kallikak/Mentor/teensy/LFOShape.png

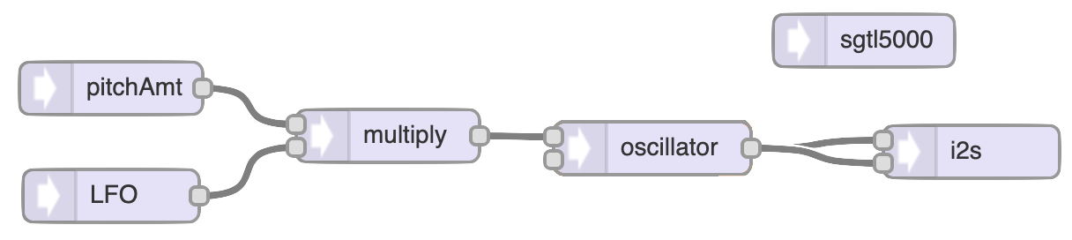
teensy/LFOShape.png
