kallikak/Mentor/teensy/WaveTypeMix.png

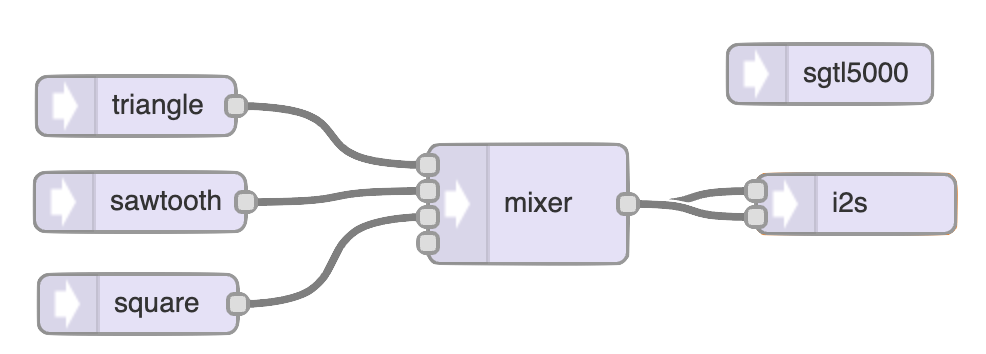
teensy/WaveTypeMix.png
